vigneshuw/aems/hardware/CustomLibs/Downloaded/SDCARD/DM3ATSFPEJM540/DM3ATSFPEJM540.stp

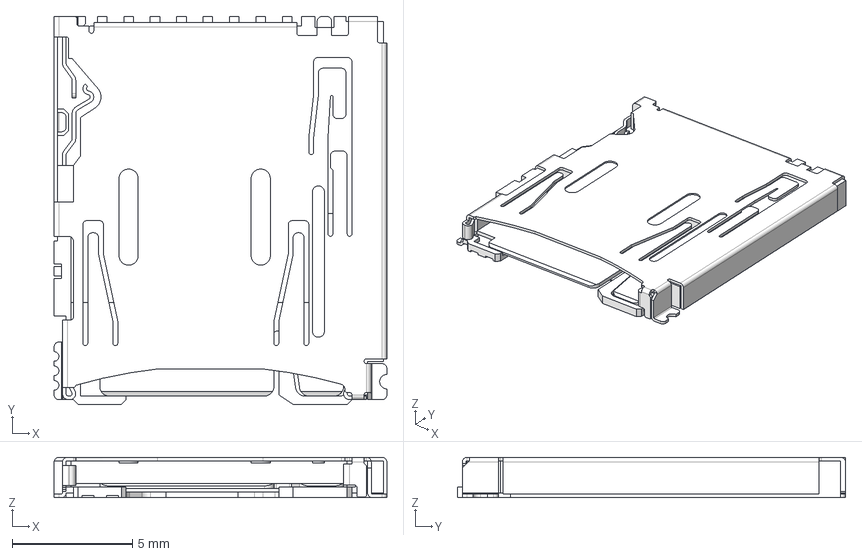
[picture p22: CAD file, 2026-07-15]
hardware/CustomLibs/Downloaded/SDCARD/DM3ATSFPEJM540/DM3ATSFPEJM540.stp
13.8 x 16.2 x 1.68 mm
