vigneshuw/aems/hardware/CustomLibs/Downloaded/SDCARD/EMIF06-MSD02N16/EMIF06-MSD02N16.stp

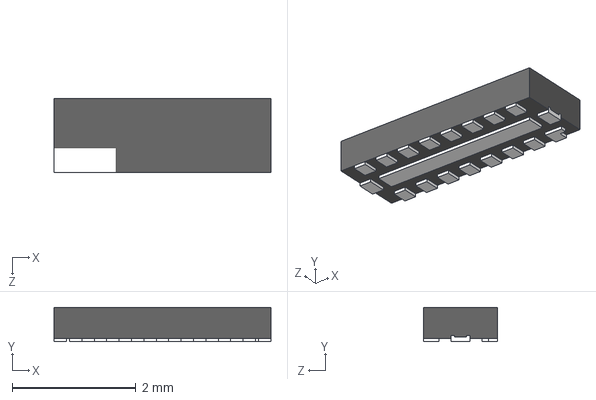
[picture p23: CAD file, 2026-07-15]
hardware/CustomLibs/Downloaded/SDCARD/EMIF06-MSD02N16/EMIF06-MSD02N16.stp
3.50 x 0.55 x 1.20 mm
