vigneshuw/aems/hardware/CustomLibs/Downloaded/TestPoint/5000/5000.stp

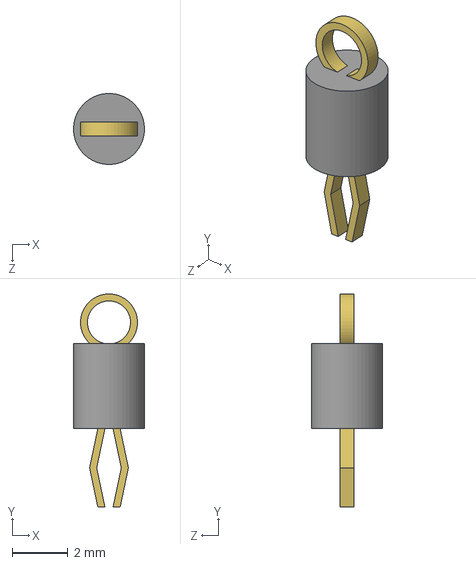
[picture p24: CAD file, 2026-07-15]
hardware/CustomLibs/Downloaded/TestPoint/5000/5000.stp
2.54 x 7.62 x 2.54 mm
