vigneshuw/aems/hardware/CustomLibs/Downloaded/uC/APFA3010LSEEZGKQBKC/APFA3010LSEEZGKQBKC.stp

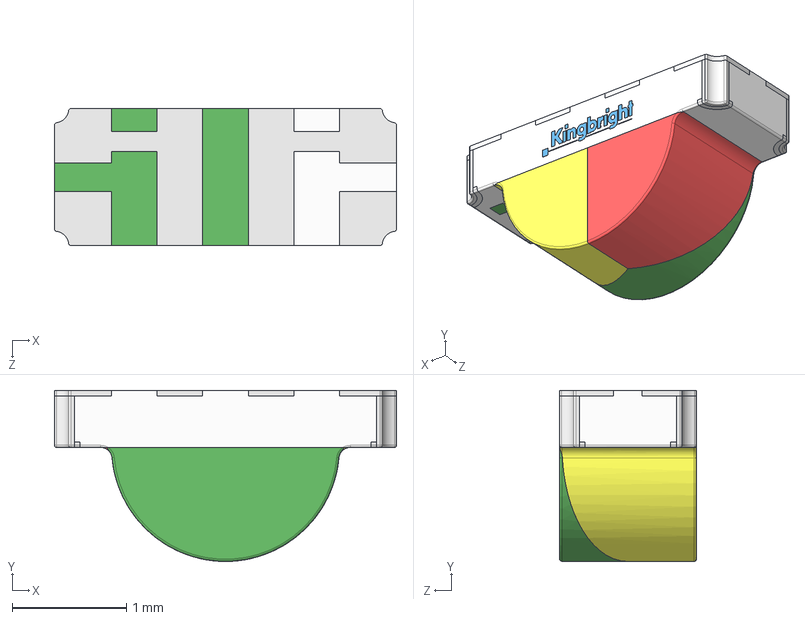
[picture p25: CAD file, 2026-07-15]
hardware/CustomLibs/Downloaded/uC/APFA3010LSEEZGKQBKC/APFA3010LSEEZGKQBKC.stp
3.00 x 1.50 x 1.20 mm
APFA3010SURKCGKSYKC
Yellow
Red
Green
Kingbright Logo
