vigneshuw/aems/hardware/CustomLibs/Downloaded/uC/PESD3V3L1BA,115/PESD3V3L1BA_115.stp

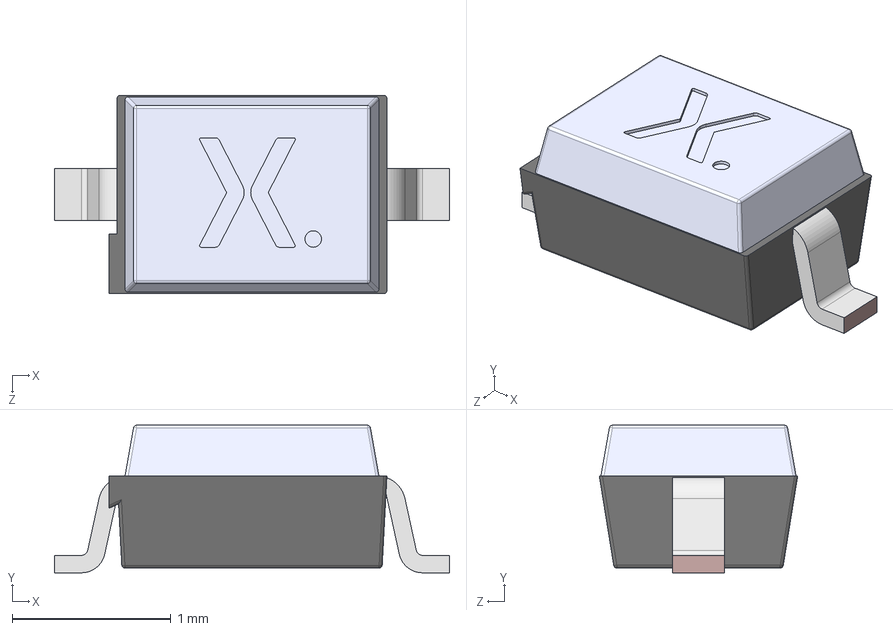
[picture p26: CAD file, 2026-07-15]
hardware/CustomLibs/Downloaded/uC/PESD3V3L1BA,115/PESD3V3L1BA_115.stp
2.49 x 0.93 x 1.25 mm
SOD323 Lower body
SOD323 Lead x 2
SOD323 Upper body
