vigneshuw/aems/hardware/CustomLibs/Downloaded/uC/STM32F103RGT6/STM32F103RGT6.stp

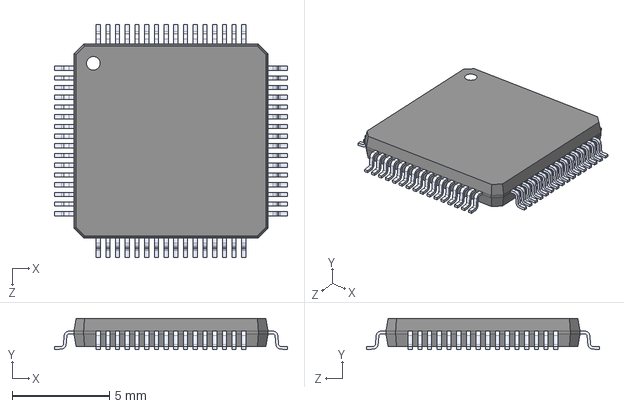
[picture p27: CAD file, 2026-07-15]
hardware/CustomLibs/Downloaded/uC/STM32F103RGT6/STM32F103RGT6.stp
12.0 x 1.60 x 12.0 mm
