vigneshuw/aems/hardware/CustomLibs/Downloaded/uCMain/STM32H745ZGT6/STM32H745ZGT6.stp

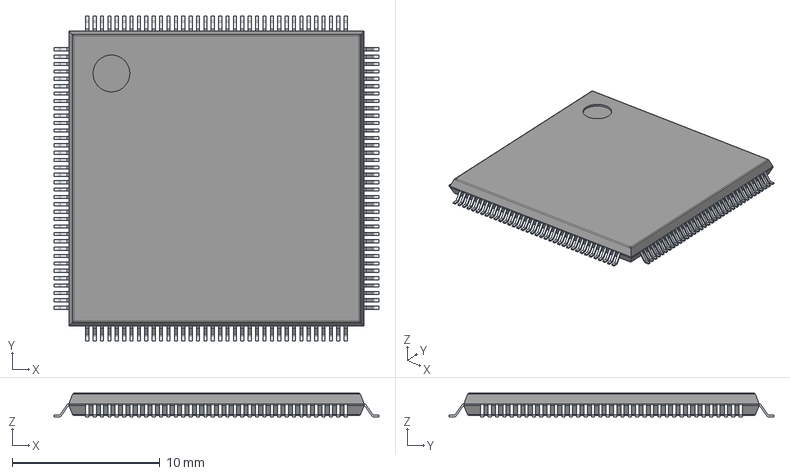
[picture p28: CAD file, 2026-07-15]
hardware/CustomLibs/Downloaded/uCMain/STM32H745ZGT6/STM32H745ZGT6.stp
22.0 x 22.0 x 1.60 mm
PinsArrayLR
PinsArrayTB
