vigneshuw/aems/hardware/CustomLibs/Downloaded/USB/BAT30KFILM/BAT30KFILM.stp

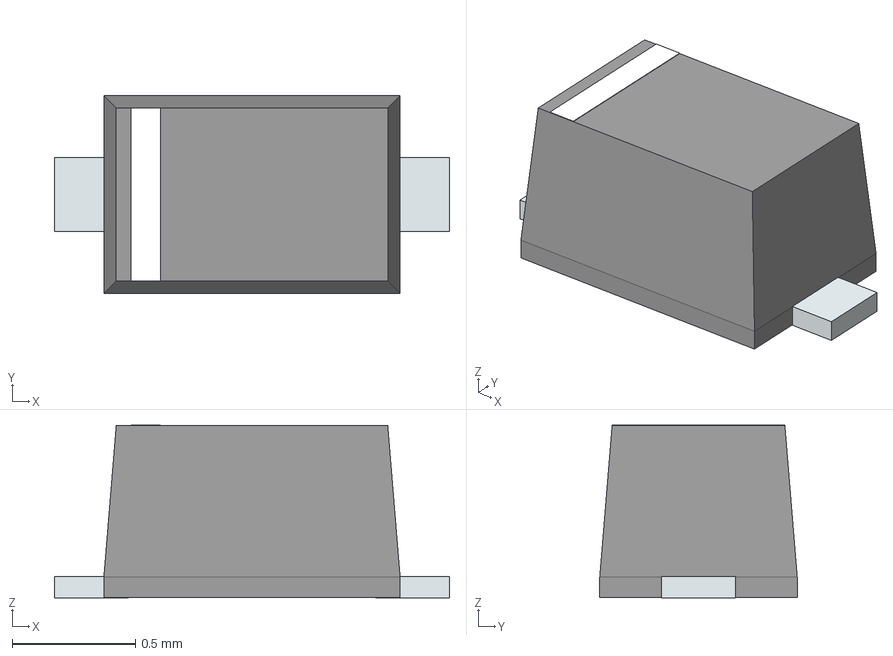
[picture p29: CAD file, 2026-07-15]
hardware/CustomLibs/Downloaded/USB/BAT30KFILM/BAT30KFILM.stp
1.60 x 0.8 x 0.7 mm
PinKIdent
PinK
PinA
