vigneshuw/aems/hardware/CustomLibs/Downloaded/USB/ESDA7P60-1U1M/ESDA7P60-1U1M.stp

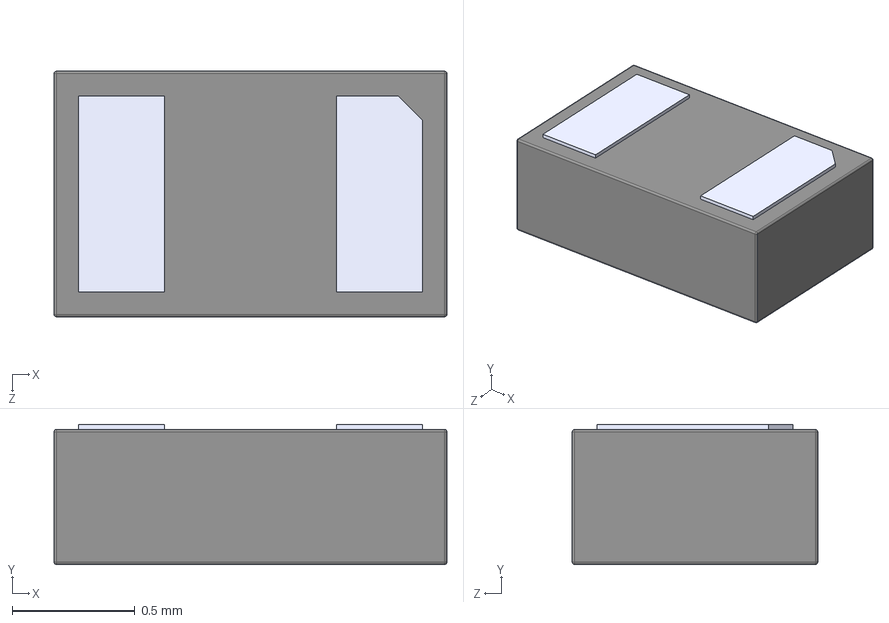
[picture p30: CAD file, 2026-07-15]
hardware/CustomLibs/Downloaded/USB/ESDA7P60-1U1M/ESDA7P60-1U1M.stp
1.60 x 0.57 x 1.00 mm
