vigneshuw/aems/hardware/CustomLibs/Downloaded/USB/STEF05SGR/STEF05SGR.stp

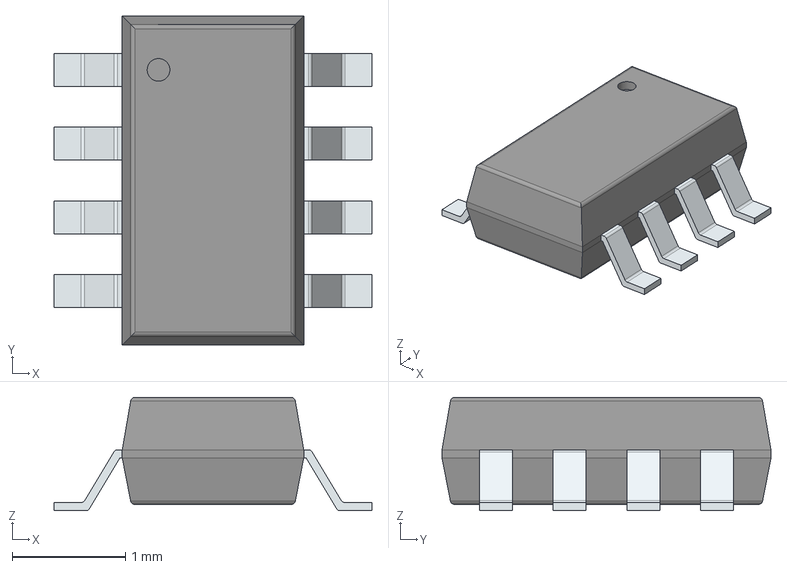
[picture p31: CAD file, 2026-07-15]
hardware/CustomLibs/Downloaded/USB/STEF05SGR/STEF05SGR.stp
2.80 x 2.90 x 1.00 mm
PinsArrayLR
