vigneshuw/aems/hardware/CustomLibs/Downloaded/USB/STL6N3LLH6/STL6N3LLH6.stp

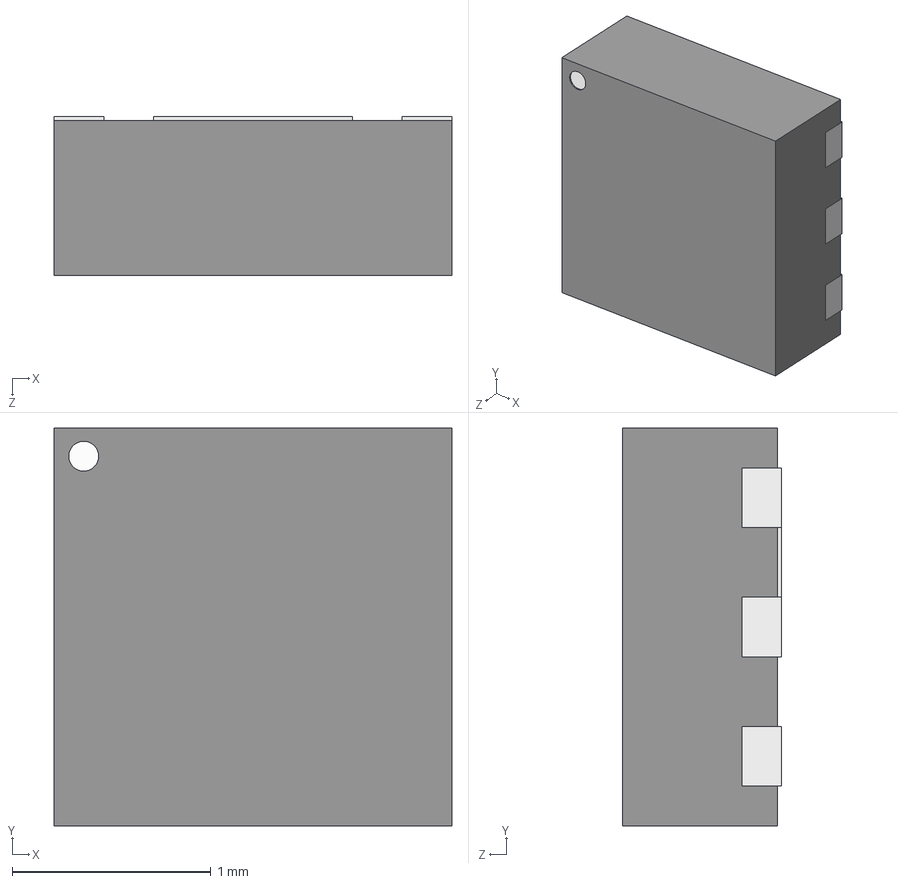
[picture p32: CAD file, 2026-07-15]
hardware/CustomLibs/Downloaded/USB/STL6N3LLH6/STL6N3LLH6.stp
2.00 x 2.00 x 0.8 mm
