vigneshuw/aems/hardware/CustomLibs/Downloaded/USB/TCPP01-M12/TCPP01-M12.stp

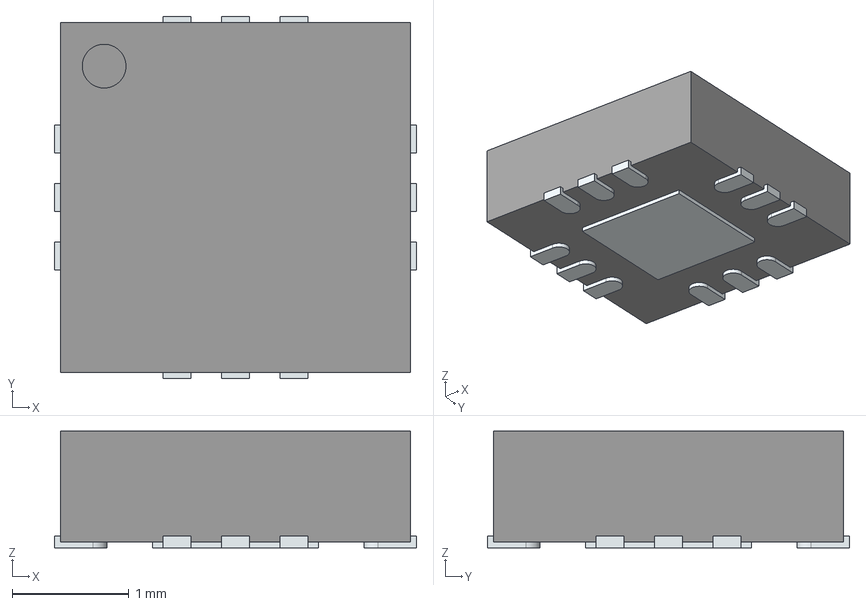
[picture p33: CAD file, 2026-07-15]
hardware/CustomLibs/Downloaded/USB/TCPP01-M12/TCPP01-M12.stp
3.10 x 3.10 x 1.00 mm
ThermalPin
PinsArrayLR
PinsArrayTB
