vigneshuw/aems/hardware/CustomLibs/Downloaded/USB/USBLC6-2P6/USBLC6-2P6.stp

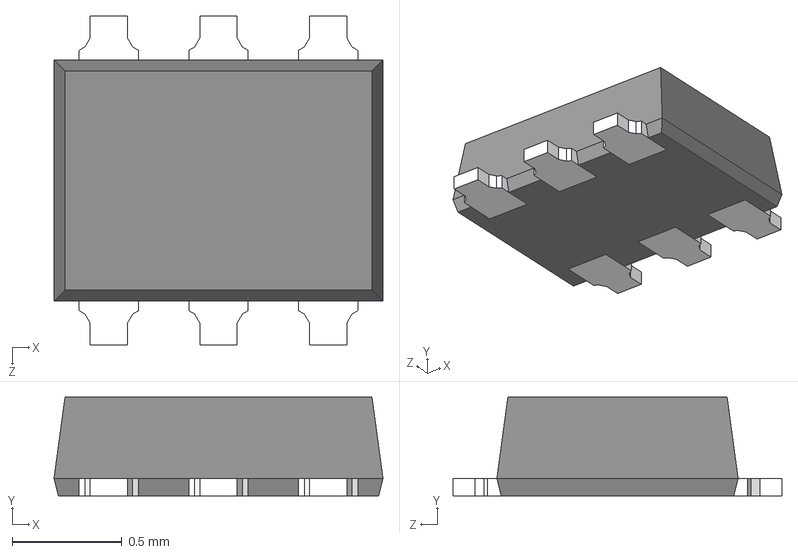
[picture p34: CAD file, 2026-07-15]
hardware/CustomLibs/Downloaded/USB/USBLC6-2P6/USBLC6-2P6.stp
1.50 x 0.45 x 1.50 mm
