vigneshuw/aems/hardware/CustomLibs/Downloaded/VR/10SVPS10M/10SVPS10M.stp

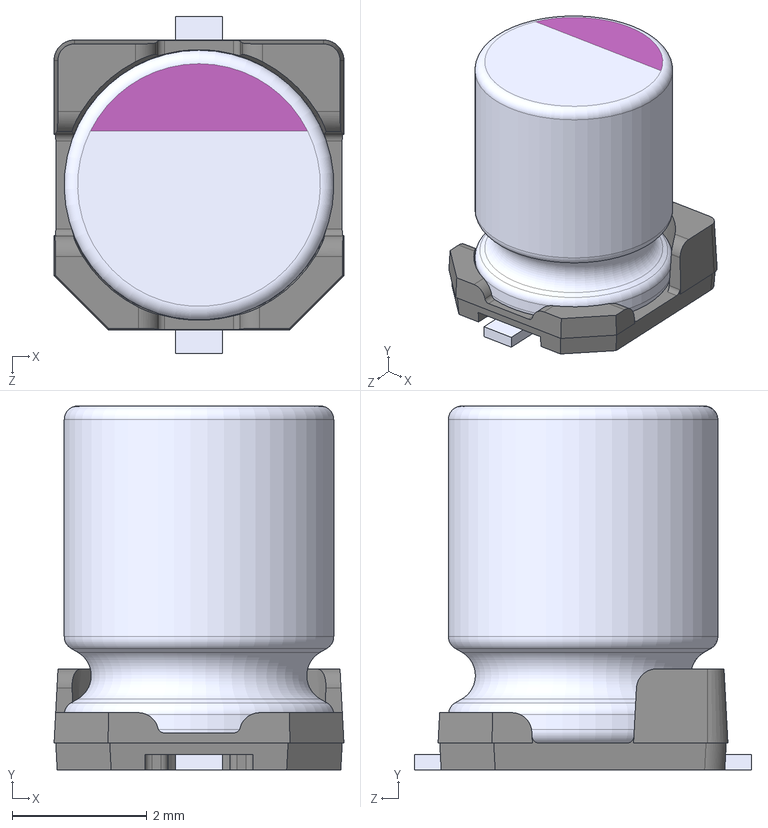
[picture p35: CAD file, 2026-07-15]
hardware/CustomLibs/Downloaded/VR/10SVPS10M/10SVPS10M.stp
4.30 x 5.40 x 5.00 mm
