vigneshuw/aems/hardware/CustomLibs/Downloaded/VR/LDLN025M12R/LDLN025M12R.stp

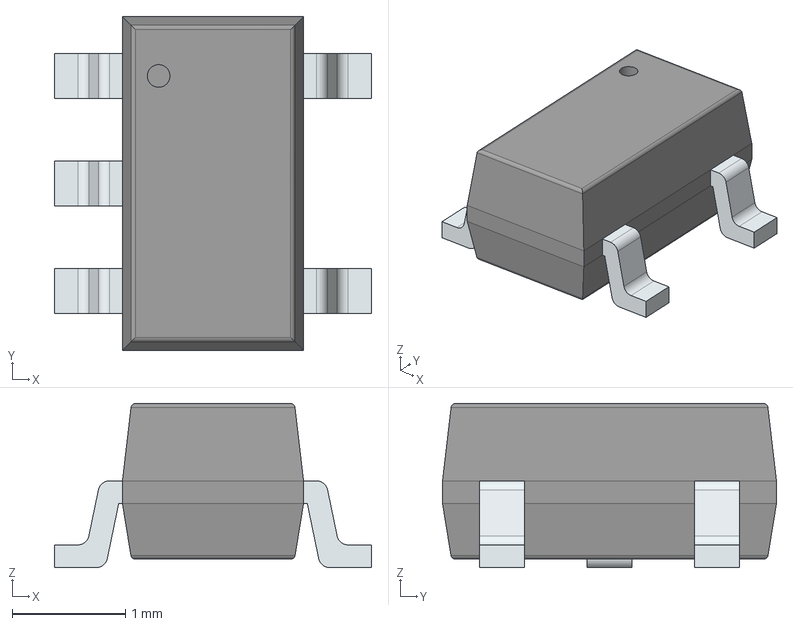
[picture p36: CAD file, 2026-07-15]
hardware/CustomLibs/Downloaded/VR/LDLN025M12R/LDLN025M12R.stp
2.80 x 2.95 x 1.45 mm
PinsArrayL
PinsArrayR
