vigneshuw/aems/hardware/CustomLibs/Downloaded/VR/LM2664M6NOPB/LM2664M6_NOPB.stp

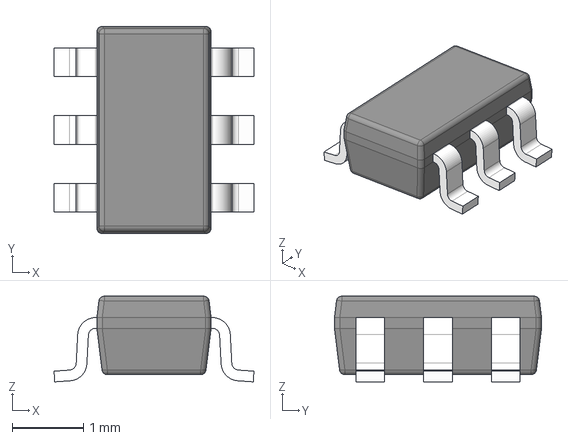
[picture p37: CAD file, 2026-07-15]
hardware/CustomLibs/Downloaded/VR/LM2664M6NOPB/LM2664M6_NOPB.stp
2.80 x 2.90 x 1.20 mm
BODY-SOT
LEAD-SOT x 6
