vigneshuw/aems/hardware/CustomLibs/Downloaded/VR/ST1PS02CQTR/ST1PS02CQTR.stp

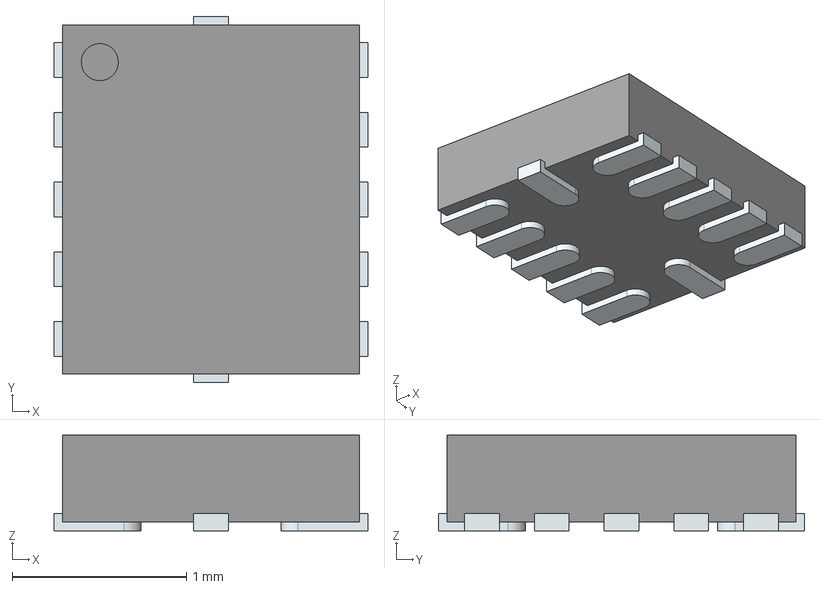
[picture p38: CAD file, 2026-07-15]
hardware/CustomLibs/Downloaded/VR/ST1PS02CQTR/ST1PS02CQTR.stp
1.80 x 2.10 x 0.55 mm
PinsArrayLR
PinsArrayTB
