vigneshuw/aems/hardware/LTSpiceSimulation/CTOpAmp/CTOpAmp.asc

C1: Cap; 10p
C2: Cap; 6800p
R7: Res; 15K
R8: Res; 10K
R9: Res; 2K
U3: TSV912
V1: voltage; SINE(0 0.4714 60)
V6: Voltage; +3.3
V7: Voltage; -3.3
Named nets: 0
.tran 0 100ms 1ms
