vigneshuw/aems/hardware/LTSpiceSimulation/Rough/CTOpAmp.asc

R3: res; 10K
R4: res; 30K
U2: AD8091
V3: voltage; +3.3
V4: voltage; -3.3
V5: Voltage; SINE(0 0.4714 60)
Named nets: 0
.tran 0 50ms 1ms
