vigneshuw/aems/hardware/LTSpiceSimulation/Rough/CTOpAmpComplete.asc

C1: Cap; 10p
C2: Cap; 6800p
R1: Res; 7.15K
R2: Res; 1K
R3: Res; 100K
R4: Res; 100K
R5: Res; 100K
R6: Res; 100K
R7: Res; 62K
R8: Res; 10K
R9: Res; 2K
U1: TSV912
U2: TSV912
U3: TSV912
V1: Voltage; 1.2
V2: Voltage; SINE(0.15 0.15 60)
V3: Voltage; +3.3
V4: Voltage; -3.3
V5: Voltage; +3.3
V6: Voltage; +3.3
V7: Voltage; -3.3
Named nets: 0
.tran 0 50ms 1ms
Voltage Buffer -> 150mV
1.2V -> 150mV
150mV
CT Input 
0 to 0.333Vac
-150mV to +150mV
Level Shifting
