vigneshuw/aems/firmware/CM4/Core/Src/sdmmc.c

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
/* Includes ------------------------------------------------------------------*/
#include "sdmmc.h"

MMC_HandleTypeDef hmmc1;

/* SDMMC1 init function */

void MX_SDMMC1_MMC_Init(void)
{

  hmmc1.Instance = SDMMC1;
  hmmc1.Init.ClockEdge = SDMMC_CLOCK_EDGE_RISING;
  hmmc1.Init.ClockPowerSave = SDMMC_CLOCK_POWER_SAVE_DISABLE;
  hmmc1.Init.BusWide = SDMMC_BUS_WIDE_8B;
  hmmc1.Init.HardwareFlowControl = SDMMC_HARDWARE_FLOW_CONTROL_DISABLE;
  hmmc1.Init.ClockDiv = 8;
  if (HAL_MMC_Init(&hmmc1) != HAL_OK)
  {
    Error_Handler();
  }
}

void HAL_MMC_MspInit(MMC_HandleTypeDef* mmcHandle)
{

  GPIO_InitTypeDef GPIO_InitStruct = {0};
  RCC_PeriphCLKInitTypeDef PeriphClkInitStruct = {0};
  if(mmcHandle->Instance==SDMMC1)
  {
  /** Initializes the peripherals clock
  */
    PeriphClkInitStruct.PeriphClockSelection = RCC_PERIPHCLK_SDMMC;
    PeriphClkInitStruct.PLL2.PLL2M = 10;
    PeriphClkInitStruct.PLL2.PLL2N = 200;
    PeriphClkInitStruct.PLL2.PLL2P = 2;
    PeriphClkInitStruct.PLL2.PLL2Q = 2;
    PeriphClkInitStruct.PLL2.PLL2R = 5;
    PeriphClkInitStruct.PLL2.PLL2RGE = RCC_PLL2VCIRANGE_1;
    PeriphClkInitStruct.PLL2.PLL2VCOSEL = RCC_PLL2VCOWIDE;
    PeriphClkInitStruct.PLL2.PLL2FRACN = 0;
    PeriphClkInitStruct.SdmmcClockSelection = RCC_SDMMCCLKSOURCE_PLL2;
    if (HAL_RCCEx_PeriphCLKConfig(&PeriphClkInitStruct) != HAL_OK)
    {
      Error_Handler();
    }

    /* SDMMC1 clock enable */
    __HAL_RCC_SDMMC1_CLK_ENABLE();

    __HAL_RCC_GPIOC_CLK_ENABLE();
    __HAL_RCC_GPIOD_CLK_ENABLE();
    __HAL_RCC_GPIOB_CLK_ENABLE();
    /**SDMMC1 GPIO Configuration
    PC6     ------> SDMMC1_D6
    PC7     ------> SDMMC1_D7
    PC8     ------> SDMMC1_D0
    PC9     ------> SDMMC1_D1
    PC10     ------> SDMMC1_D2
    PC11     ------> SDMMC1_D3
    PC12     ------> SDMMC1_CK
    PD2     ------> SDMMC1_CMD
    PB8     ------> SDMMC1_D4
    PB9     ------> SDMMC1_D5
    */
    GPIO_InitStruct.Pin = GPIO_PIN_6|GPIO_PIN_7|GPIO_PIN_8|GPIO_PIN_9
                          |GPIO_PIN_10|GPIO_PIN_11|GPIO_PIN_12;
    GPIO_InitStruct.Mode = GPIO_MODE_AF_PP;
    GPIO_InitStruct.Pull = GPIO_NOPULL;
    GPIO_InitStruct.Speed = GPIO_SPEED_FREQ_VERY_HIGH;
    GPIO_InitStruct.Alternate = GPIO_AF12_SDIO1;
    HAL_GPIO_Init(GPIOC, &GPIO_InitStruct);

    GPIO_InitStruct.Pin = GPIO_PIN_2;
    GPIO_InitStruct.Mode = GPIO_MODE_AF_PP;
    GPIO_InitStruct.Pull = GPIO_NOPULL;
    GPIO_InitStruct.Speed = GPIO_SPEED_FREQ_VERY_HIGH;
    GPIO_InitStruct.Alternate = GPIO_AF12_SDIO1;
    HAL_GPIO_Init(GPIOD, &GPIO_InitStruct);

    GPIO_InitStruct.Pin = GPIO_PIN_8|GPIO_PIN_9;
    GPIO_InitStruct.Mode = GPIO_MODE_AF_PP;
    GPIO_InitStruct.Pull = GPIO_NOPULL;
    GPIO_InitStruct.Speed = GPIO_SPEED_FREQ_VERY_HIGH;
    GPIO_InitStruct.Alternate = GPIO_AF12_SDIO1;
    HAL_GPIO_Init(GPIOB, &GPIO_InitStruct);

  }
}

void HAL_MMC_MspDeInit(MMC_HandleTypeDef* mmcHandle)
{

  if(mmcHandle->Instance==SDMMC1)
  {
    /* Peripheral clock disable */
    __HAL_RCC_SDMMC1_CLK_DISABLE();

    /**SDMMC1 GPIO Configuration
    PC6     ------> SDMMC1_D6
    PC7     ------> SDMMC1_D7
    PC8     ------> SDMMC1_D0
    PC9     ------> SDMMC1_D1
    PC10     ------> SDMMC1_D2
    PC11     ------> SDMMC1_D3
    PC12     ------> SDMMC1_CK
    PD2     ------> SDMMC1_CMD
    PB8     ------> SDMMC1_D4
    PB9     ------> SDMMC1_D5
    */
    HAL_GPIO_DeInit(GPIOC, GPIO_PIN_6|GPIO_PIN_7|GPIO_PIN_8|GPIO_PIN_9
                          |GPIO_PIN_10|GPIO_PIN_11|GPIO_PIN_12);

    HAL_GPIO_DeInit(GPIOD, GPIO_PIN_2);

    HAL_GPIO_DeInit(GPIOB, GPIO_PIN_8|GPIO_PIN_9);

  }
}

/* USER CODE BEGIN 1 */
HAL_StatusTypeDef SDMMC1_SetClockDiv(uint32_t clock_div)
{
  if (hmmc1.Instance != SDMMC1)
  {
    return HAL_ERROR;
  }

  if (clock_div > 0x3FFU)
  {
    return HAL_ERROR;
  }

  hmmc1.Init.ClockDiv = clock_div;
  MODIFY_REG(hmmc1.Instance->CLKCR, SDMMC_CLKCR_CLKDIV, clock_div);
  return HAL_OK;
}

uint32_t SDMMC1_GetClockDiv(void)
{
  return READ_BIT(hmmc1.Instance->CLKCR, SDMMC_CLKCR_CLKDIV);
}

/* USER CODE END 1 */
