vigneshuw/aems/firmware/CM4/OPENAMP/rsc_table.h

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

/* This file populates resource table for BM remote
 * for use by the Linux Master */
/* USER CODE END Header */

#ifndef RSC_TABLE_H_
#define RSC_TABLE_H_

#include "openamp/open_amp.h"
#include "openamp_conf.h"

/* Exported types ------------------------------------------------------------*/
/* USER CODE BEGIN ET */

/* Resource table for the given remote */
struct shared_resource_table {
	unsigned int version;
	unsigned int num;
	unsigned int reserved[2];
	unsigned int offset[NUM_RESOURCE_ENTRIES];
	/* text carveout entry */

	/* rpmsg vdev entry */
	struct fw_rsc_vdev vdev;
	struct fw_rsc_vdev_vring vring0;
	struct fw_rsc_vdev_vring vring1;
	struct fw_rsc_trace cm_trace;
};

/* USER CODE END ET */

/* Exported constants --------------------------------------------------------*/
/* USER CODE BEGIN Private defines */

/* USER CODE END  Private defines */

/* Exported macro ------------------------------------------------------------*/
/* Exported functions prototypes ---------------------------------------------*/
void resource_table_init(int RPMsgRole, void **table_ptr, int *length);

#endif /* RSC_TABLE_H_ */
